sparkfun/SparkFun_6DoF_LSM6DSV16X/docs/assets/imgs/Example4_Output.jpg

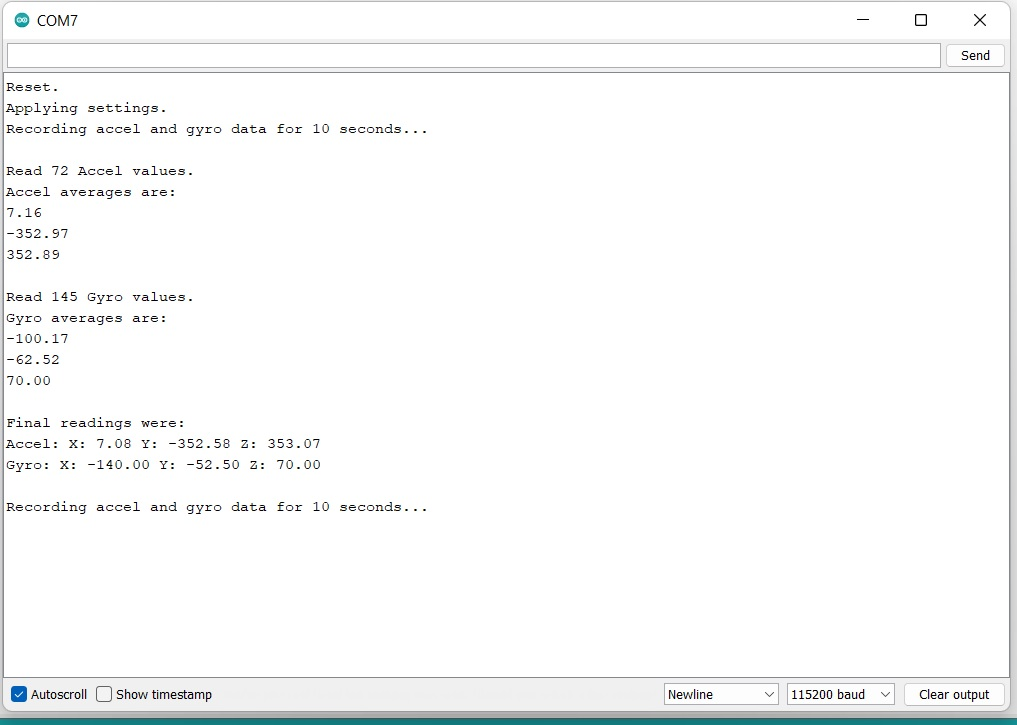
docs/assets/imgs/Example4_Output.jpg
